afbento/tec_mec_hotbit_msx/photos/estab_ideal.JPG

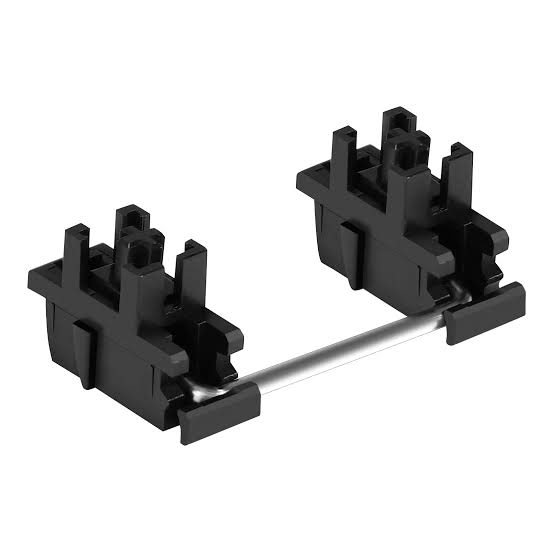
photos/estab_ideal.JPG
