afbento/tec_mec_hotbit_msx/photos/gabar_ruim_adapt.JPG

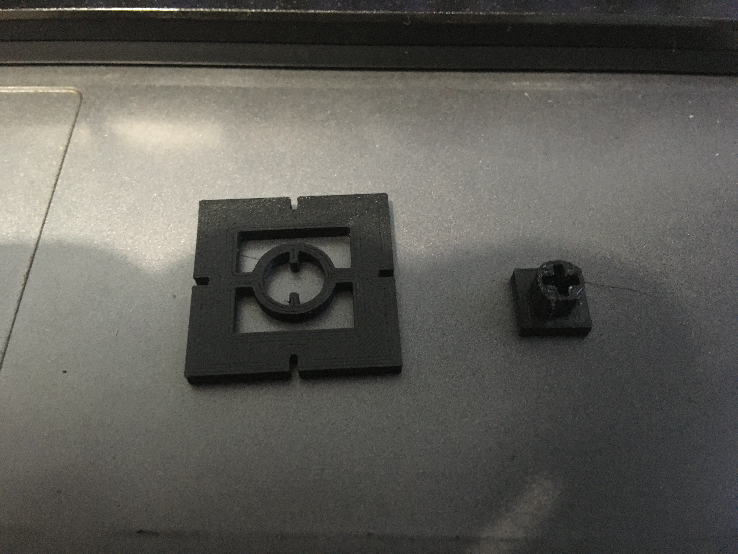
photos/gabar_ruim_adapt.JPG
